mcbittech/souliss-smart-thermostat-WiFi/Libraries-Core-Docs/docs/11448259.png

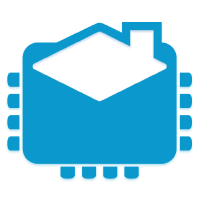
Libraries-Core-Docs/docs/11448259.png
