mcbittech/souliss-smart-thermostat-WiFi/Libraries-Core-Docs/Connection/SST.sch

## EAGLE design Libraries-Core-Docs/Connection/SST.sch (2015-10-02)

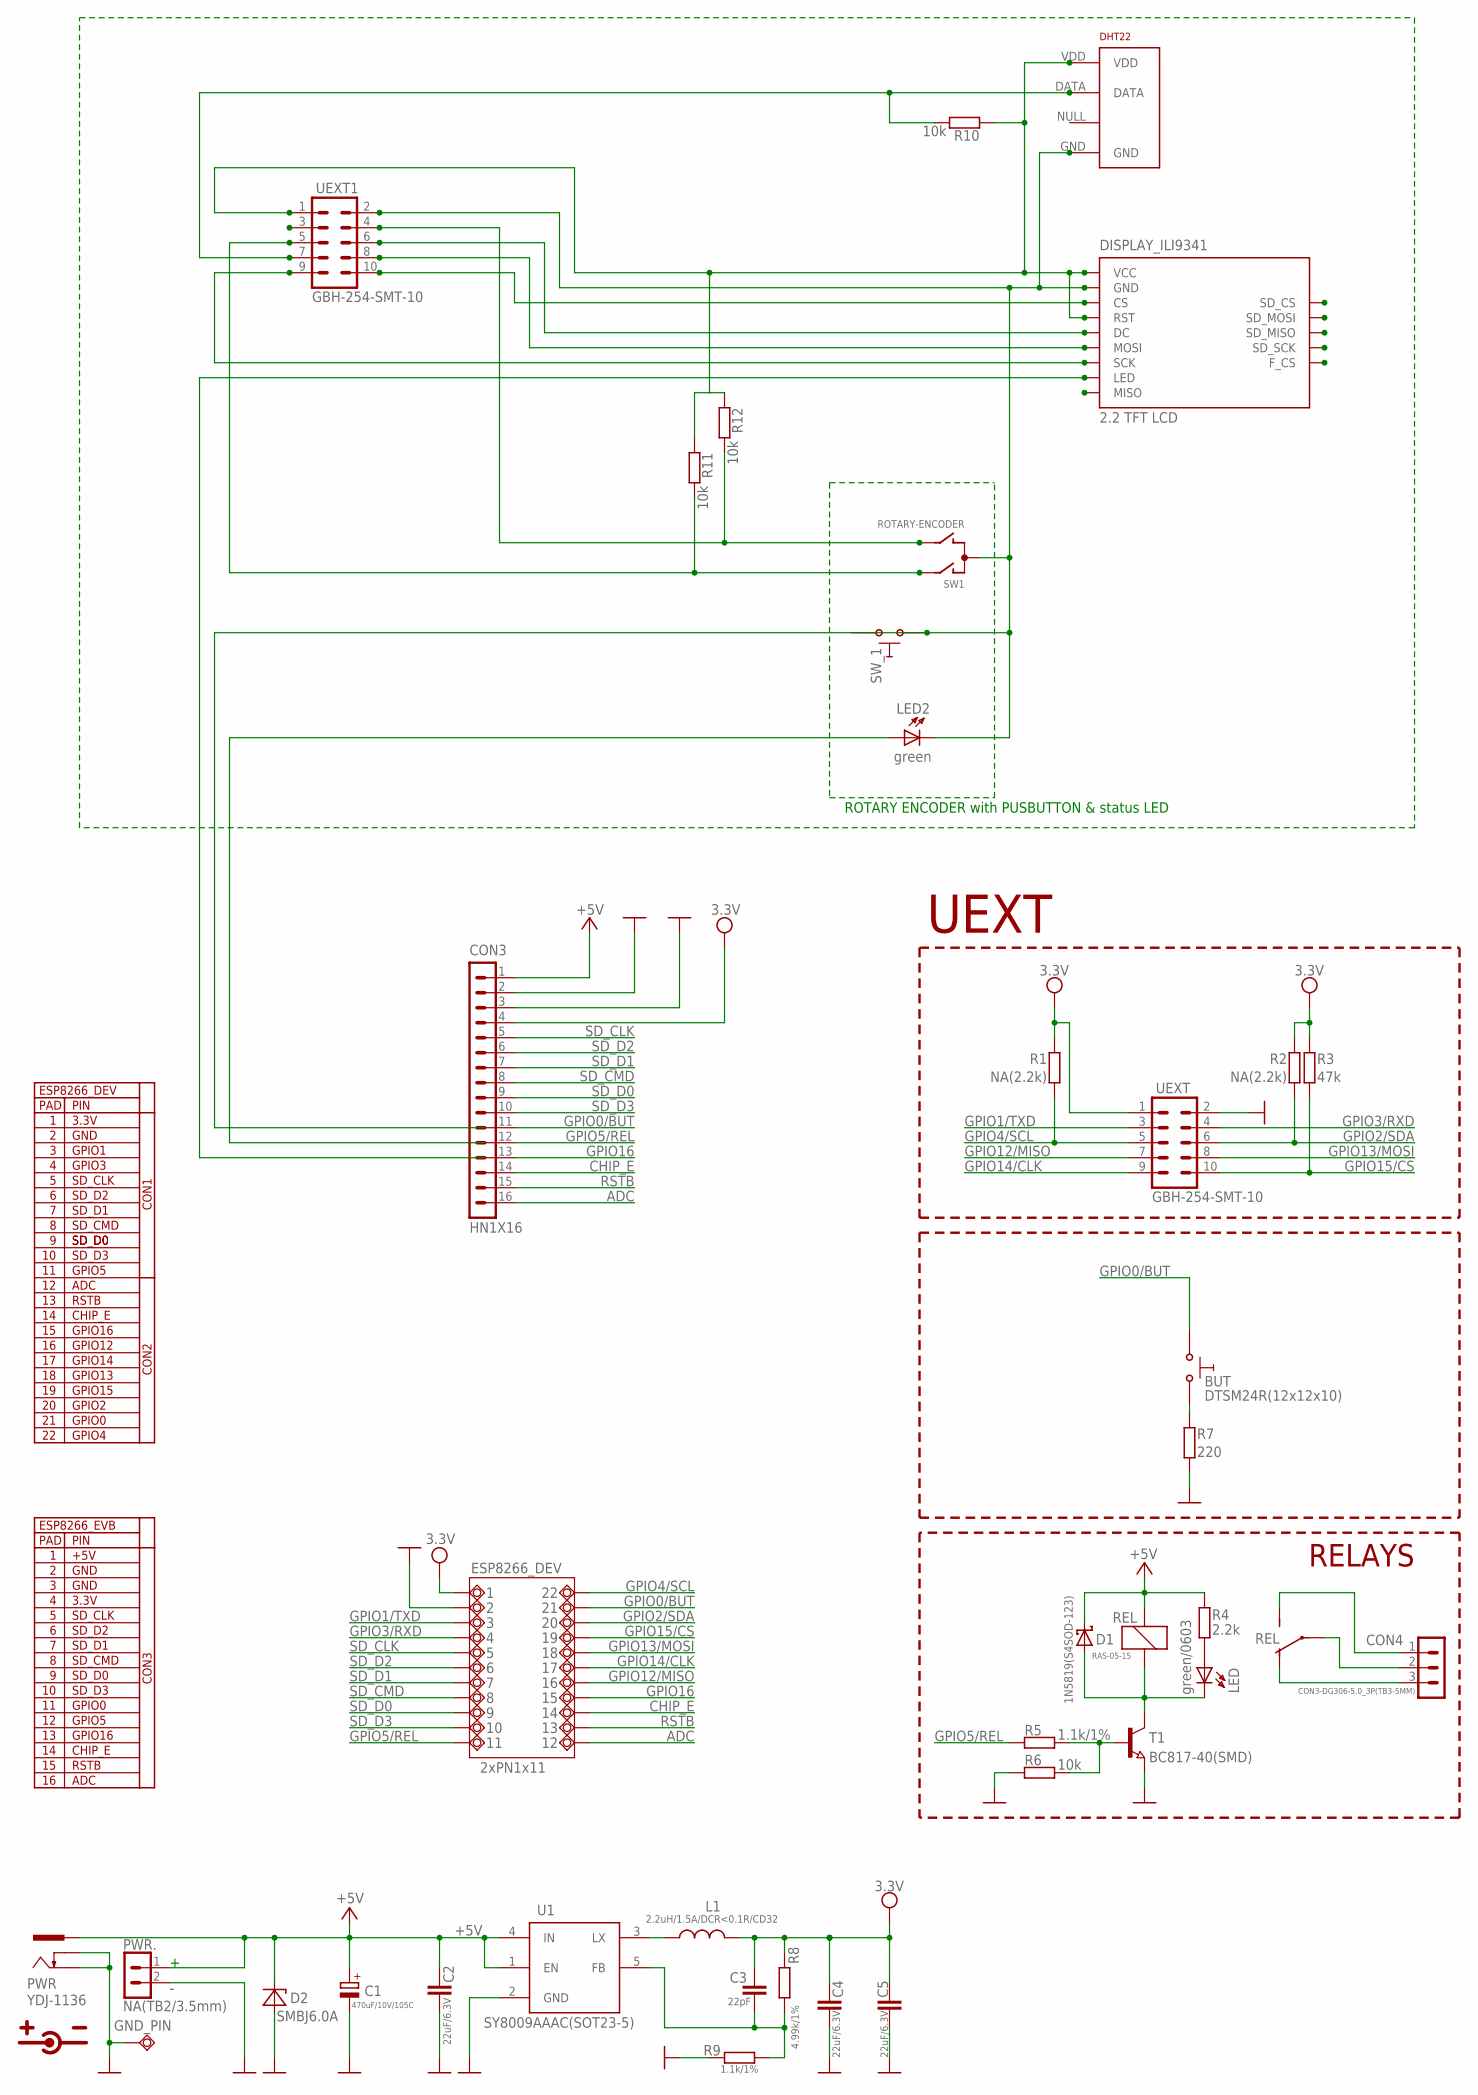
[picture p16: schematic SST.sch]

Parts:
1: TESTPAD40/60/SQUARE; TESTPAD40/66/SQUARE
2, 3, 4, 5, 6, 7, 8, 9, 10, 11, 12, 13, 14, 15, 16, 17, 18, 19, 20, 21, 22: TESTPAD40/66
BUT: DTSM24R(12x12x10); SW_TAKT12X12SS
C1: 470uF/10V/105C; E2,5-6,3
C2, C4, C5: 22uF/6.3V; C0603_DWS
C3: 22pF; C0603_DWS
CON3: HN1X16
CON4: CON3-DG306-5.0_3P(TB3-5MM); DG306-5.0_3P
D1: 1N5819(S4SOD-123); SOD-123
D2: SMBJ6.0A; DO214AA
DHT22: RHT03_DHT-22_AM2302RA; RHT03_DHT-22/RA
DISPLAY_ILI9341: 2.2_TFT_LCD
GND_PIN: TESTPAD3; TEST_PAD40/70/SQUARE
L1: 2.2uH/1.5A/DCR<0.1R/CD32; CD32
LED: green/0603; LED-0603_L
LED2: green; LED-0603_L
PWR: YDJ-1136; PWR_JACK_UNI_MILLING
PWR.: NA(TB2/3.5mm); DG306-5.0_2P
R1, R2: NA(2.2k); R0603_5MIL_DWS
R3: 47k; R0603_5MIL_DWS
R4: 2.2k; R0603_5MIL_DWS
R5, R9: 1.1k/1%; R0603_5MIL_DWS
R6, R10, R11, R12: 10k; R0603_5MIL_DWS
R7: 220; R0603_5MIL_DWS
R8: 4.99k/1%; R0603_5MIL_DWS
REL: RAS-05-15; H200-FAT
SW1: ROTARY-ENCODER; ALPS_EC12E_SW
SW_1: SW-TAKTSS; SW_TAKT12X12SS
T1: BC817-40(SMD); SOT23
U1: SY8009AAAC(SOT23-5); SOT23-5
UEXT, UEXT1: GBH-254-SMT-10; ML10-MALE

Connections:
+5V: C1.+, C2.1, CON3.1, D1.C, D2.C, PWR.+, PWR..1, R4.2, REL.1, U1.1 (EN), U1.4 (IN)
ADC: 12.P$1, CON3.16
CHIP_E: 14.P$1, CON3.14
COM: CON4.2, REL.P
GND: 2.P$1, C1.-, C2.2, C4.2, C5.2, CON3.2, CON3.3, D2.A, GND_PIN.P$1, PWR.-, PWR.--, PWR..2, R6.2, R7.1, R9.2, T1.2 (E), U1.2 (GND), UEXT.2
GPIO0/BUT: 21.P$1, BUT.P$2 (1), CON3.11
GPIO1/TXD: 3.P$1, UEXT.3
GPIO2/SDA: 20.P$1, R2.1, UEXT.6
GPIO3/RXD: 4.P$1, UEXT.4
GPIO4/SCL: 22.P$1, R1.1, UEXT.5
GPIO5/REL: 11.P$1, CON3.12, R5.2
GPIO12/MISO: 16.P$1, UEXT.7
GPIO13/MOSI: 18.P$1, UEXT.8
GPIO14/CLK: 17.P$1, UEXT.9
GPIO15/CS: 19.P$1, R3.1, UEXT.10
GPIO16: 15.P$1, CON3.13
unnamed: LED.A, R4.1
unnamed: R11.1, SW1.A, UEXT1.5
unnamed: DHT22.VDD, DISPLAY_ILI9341.RST, DISPLAY_ILI9341.VCC, R10.2, R11.2, R12.2, UEXT1.1
unnamed: R12.1, SW1.B, UEXT1.4
unnamed: DHT22.GND, DISPLAY_ILI9341.GND, LED2.C, SW1.C, SW_1.P$1 (0), SW_1.P$2 (1), UEXT1.2
unnamed: DISPLAY_ILI9341.CS, UEXT1.10
unnamed: DISPLAY_ILI9341.DC, UEXT1.6
unnamed: DISPLAY_ILI9341.MOSI, UEXT1.8
unnamed: DISPLAY_ILI9341.SCK, UEXT1.9
unnamed: R5.1, R6.1, T1.1 (B)
unnamed: DHT22.DATA, R10.1, UEXT1.7
unnamed: BUT.P$1 (0), R7.2
unnamed: D1.A, LED.C, REL.2, T1.3 (C)
unnamed: L1.1, U1.3 (LX)
unnamed: C3.2, R8.2, R9.1, U1.5 (FB)
NC: CON4.3, REL.O
NO: CON4.1, REL.S
RSTB: 13.P$1, CON3.15
SD_CLK: 5.P$1, CON3.5
SD_CMD: 8.P$1, CON3.8
SD_D0: 9.P$1, CON3.9
SD_D1: 7.P$1, CON3.7
SD_D2: 6.P$1, CON3.6
SD_D3: 10.P$1, CON3.10
VCC: 1.P$1, C3.1, C4.1, C5.1, CON3.4, L1.2, R1.2, R2.2, R3.2, R8.1, UEXT.1

Notes on the sheet:
PAD
GPIO1
GPIO3
SD_CLK
SD_D0
SD_D1
SD_D2
SD_D3
SD_CMD
3.3V
GND
GPIO5
GPIO4
GPIO0
GPIO2
GPIO15
GPIO13
GPIO12
GPIO14
GPIO16
ADC
PIN
RSTB
CHIP_E
RELAYS
UEXT
ESP8266_DEV
CON1
CON2
ESP8266_EVB
CON3
+5V
2xPN1x11
ROTARY ENCODER with PUSBUTTON & status LED
