mcbittech/souliss-smart-thermostat-WiFi/SST_Eclipse/SST_Eclipse/encoder.h

//ENCODER
////////////////////////////////////////////////////////////////////////////////////////////////////////////////
#include <Arduino.h>

float getEncoderValue();
float getEncoderValueSlow();
void setEncoderValue(float);
void encoder();
