mcbittech/souliss-smart-thermostat-WiFi/SST_Eclipse/SST_Eclipse/connection_static.h

/*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
    Modified by Dario Di Maio, original code from
       https://github.com/esp8266/Arduino

***************************************************************************/
uint8_t static_ip_address[4]  = {STATIC_IP}; 
uint8_t static_subnet_mask[4] = {STATIC_SUBNET};
uint8_t static_ip_gateway[4]  = {STATIC_IP_GW}; 

#define STATIC_CONNECTION_Init_DHCP()              \
  SERIAL_OUT.println("start STATIC_CONNECTION_Init_DHCP"); \
  display_print_splash_connection_to_home_wifi(ucg); \
  /** Connect to the WiFi network and get an address from DHCP*/ \
  GetIPAddress(); \
  SERIAL_OUT.println("Address received"); \
  /** This is the vNet address for this node, used to communicate with other */ \
  /** nodes in your Souliss network*/ \
  SetAddress(peer_address, myvNet_subnet, wifi_bridge_address);          /* Address on the wireless interface*/ \
  
#define STATIC_CONNECTION_Init_STATICIP()              \
  SERIAL_OUT.println("start STATIC_CONNECTION_Init_STATICIP"); \
  SetIPAddress(static_ip_address, static_subnet_mask, static_ip_gateway); \
  display_print_splash_connection_to_home_wifi(ucg); \
  SetAddress(peer_address, myvNet_subnet, wifi_bridge_address); \
  SERIAL_OUT.println("Address set from preferences"); \
  
#define STATIC_CONNECTION_fast()       \
FAST_PeerComms();\
