mcbittech/souliss-smart-thermostat-WiFi/e06_ESP_SST_RemoteHeatingRelay/topics.h

#include <Arduino.h>

//PUBLISH&SUBSCRIBE TOPICS
////////////////////////////////////////////////////////////////////////////////////////////////////////////////

#define SST_HEAT_ONOFF 0xF001,0x0B
U8 HEAT_ON = 0X01;
U8 HEAT_OFF = 0X00;
