mcbittech/souliss-smart-thermostat-WiFi/SST_Eclipse/SST_Eclipse/topics.h

#include <Arduino.h>

//PUBLISH&SUBSCRIBE TOPICS
////////////////////////////////////////////////////////////////////////////////////////////////////////////////
#define TOPIC1 0xF001,0x05
#define TOPIC2 0xF001,0x06
#define TOPIC3 0xF001,0x07
#define TOPIC4 0xF001,0x08
#define TOPIC5 0xF001,0x09
#define TOPIC6 0xF001,0x0A

#define SST_HEAT_ONOFF 0xF001,0x0B
U8 HEAT_ON = 0X01;
U8 HEAT_OFF = 0X00;

//*****************************************************
//  ES:
//#define TEMPERATURE_TOPIC_NODE_DHT_RELE 0xF001,0x15
//#define HUMIDITY_TOPIC_NODE_DHT_RELE 0xF001,0x16
